takashicompany/jourkey/images/01.jpg

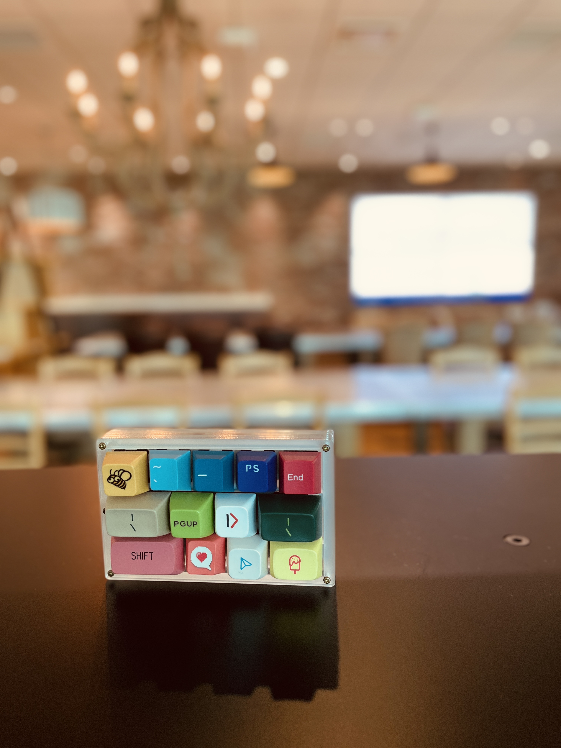
images/01.jpg
