takashicompany/jourkey/images/02.jpg

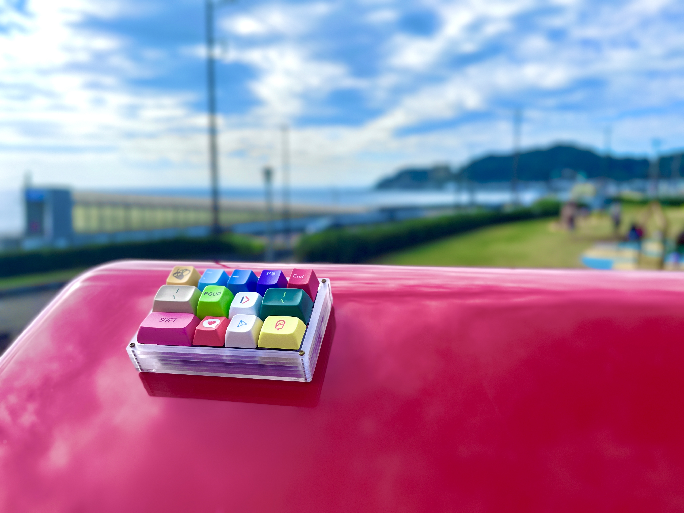
images/02.jpg
