takashicompany/jourkey/images/04.jpg

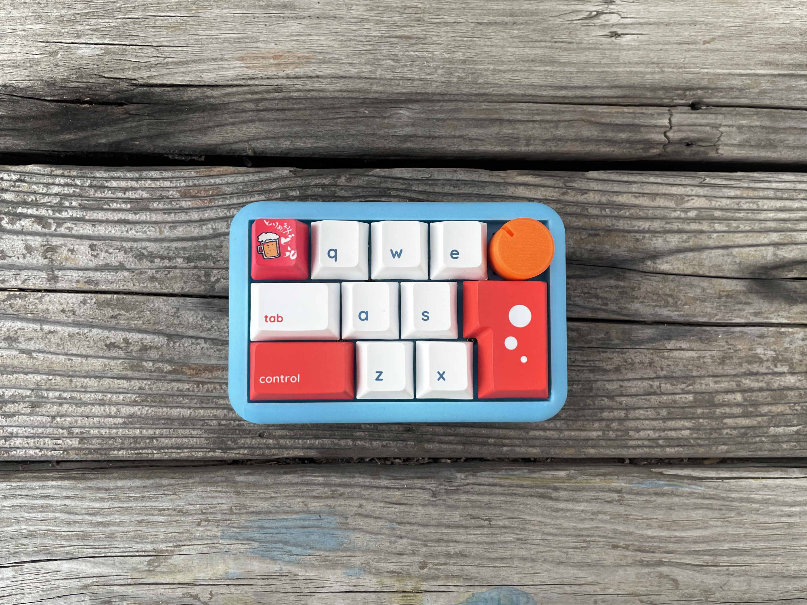
images/04.jpg
