takashicompany/jourkey/images/build/IMG_0001.jpg

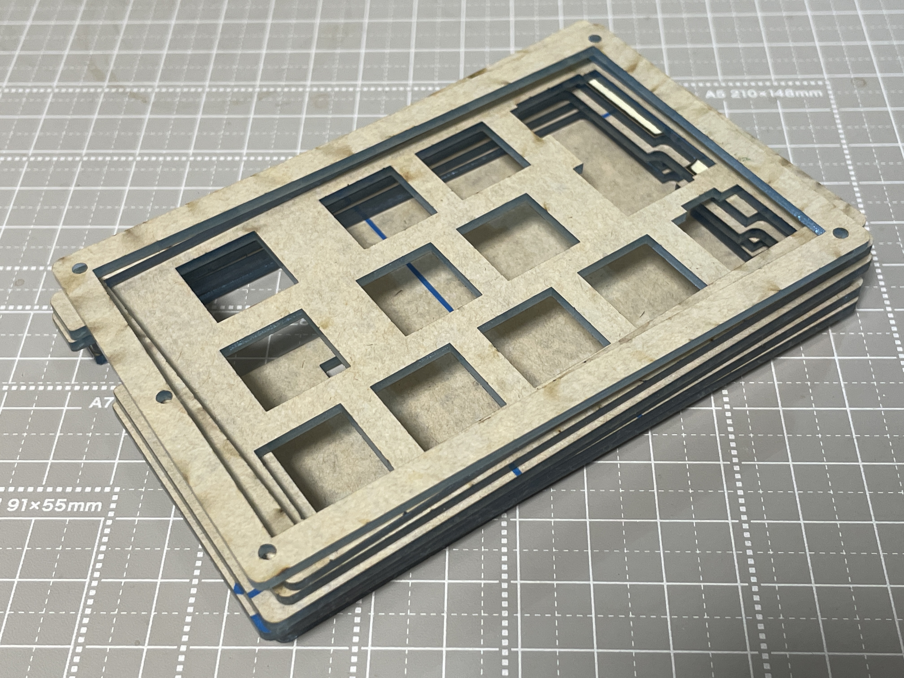
images/build/IMG_0001.jpg
