takashicompany/jourkey/images/build/IMG_0002.jpg

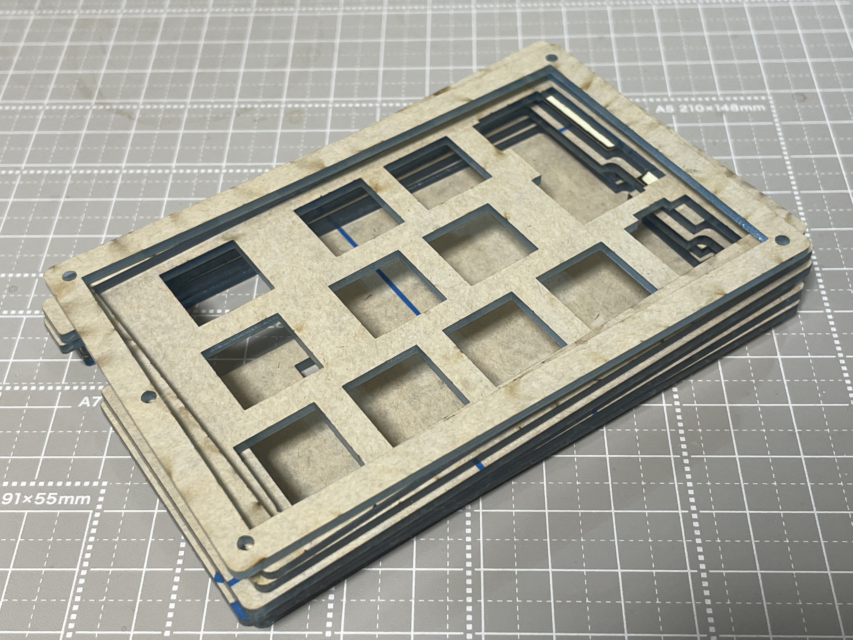
images/build/IMG_0002.jpg
