takashicompany/jourkey/images/build/IMG_0005.jpg

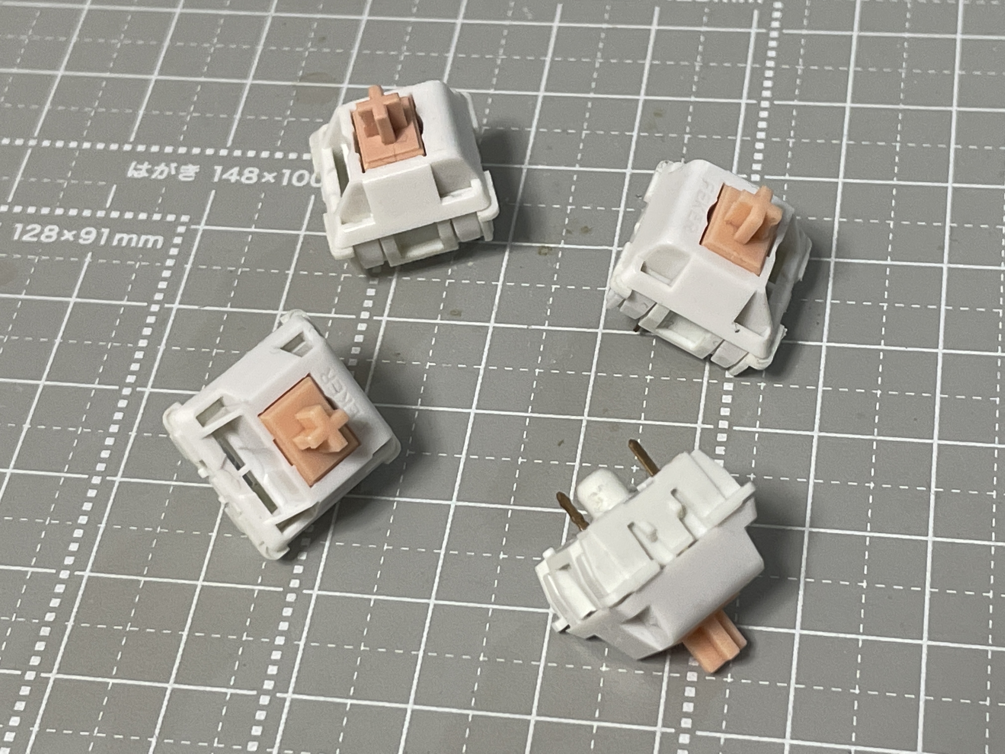
images/build/IMG_0005.jpg
