takashicompany/jourkey/images/build/IMG_0006.jpg

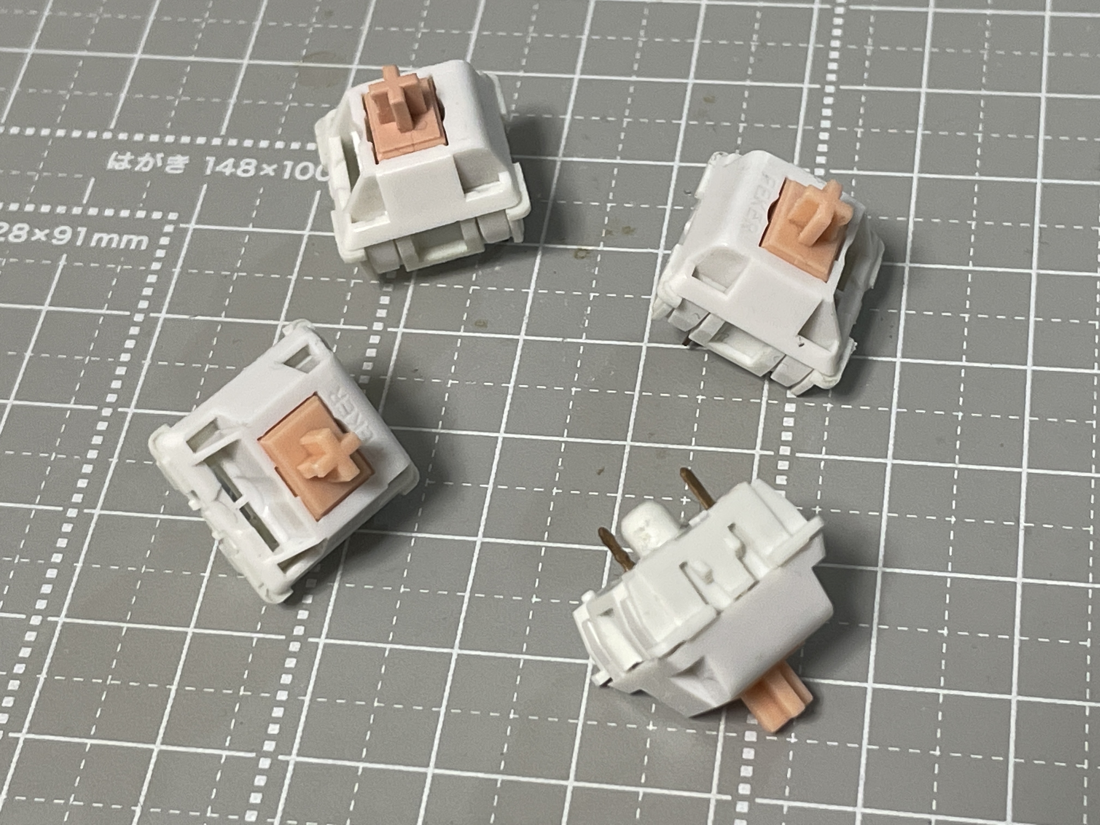
images/build/IMG_0006.jpg
