takashicompany/jourkey/images/build/IMG_0008.jpg

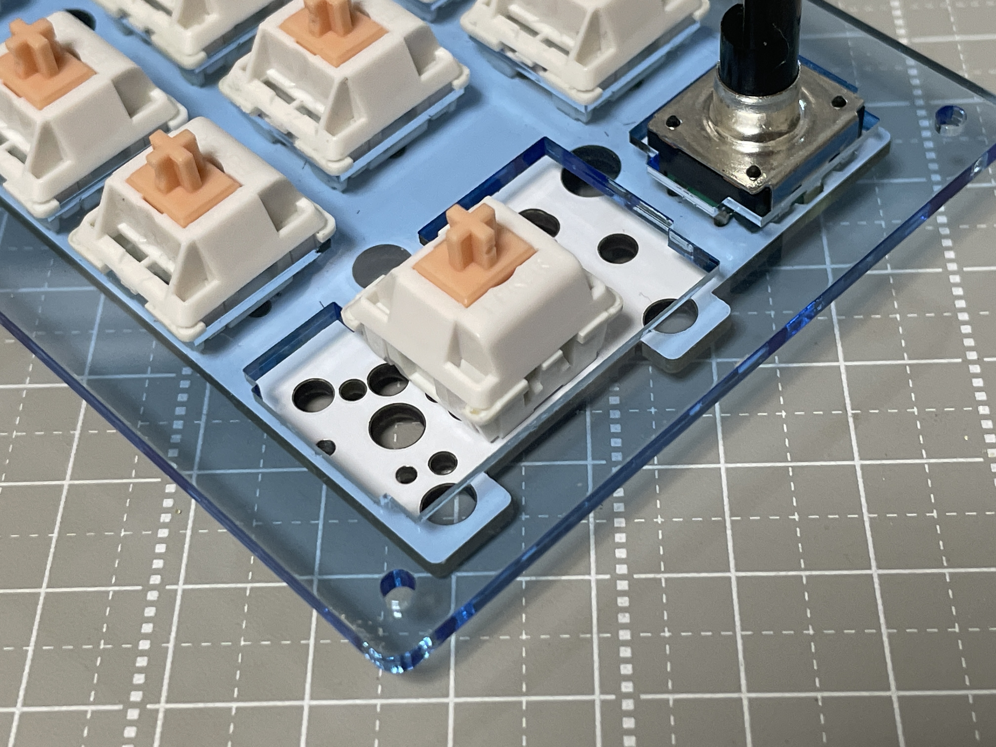
images/build/IMG_0008.jpg
