takashicompany/jourkey/images/build/IMG_0010.jpg

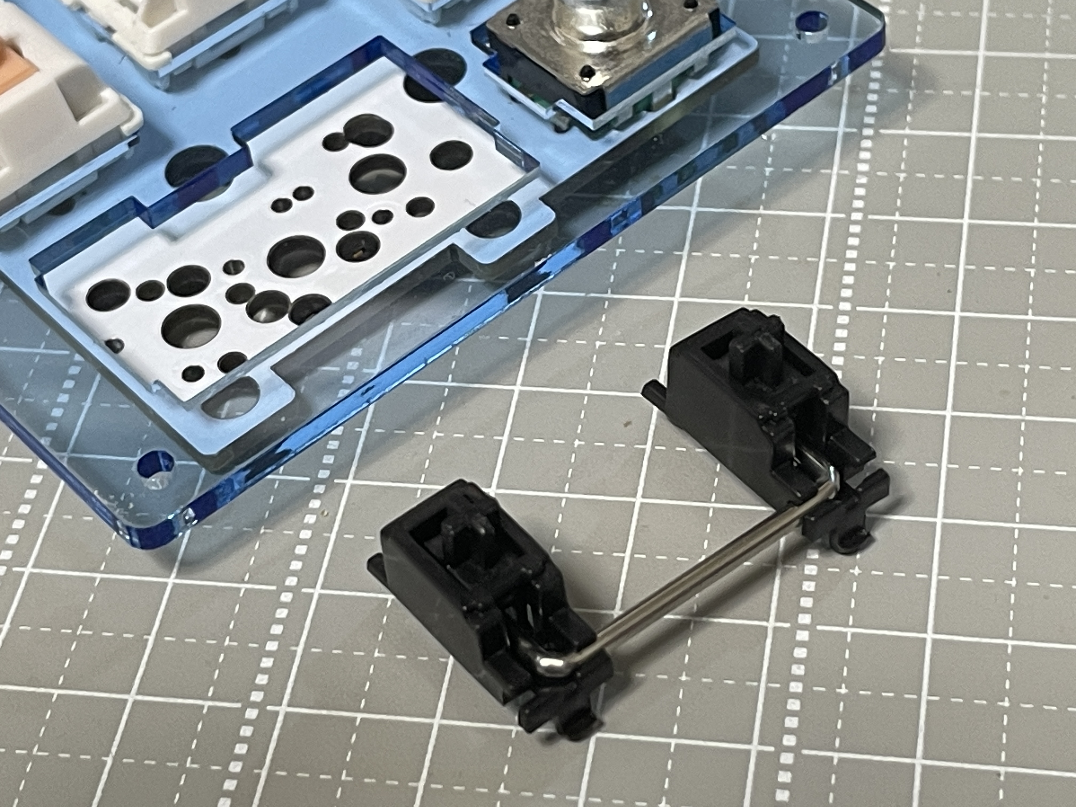
images/build/IMG_0010.jpg
