takashicompany/jourkey/images/build/IMG_0012.jpg

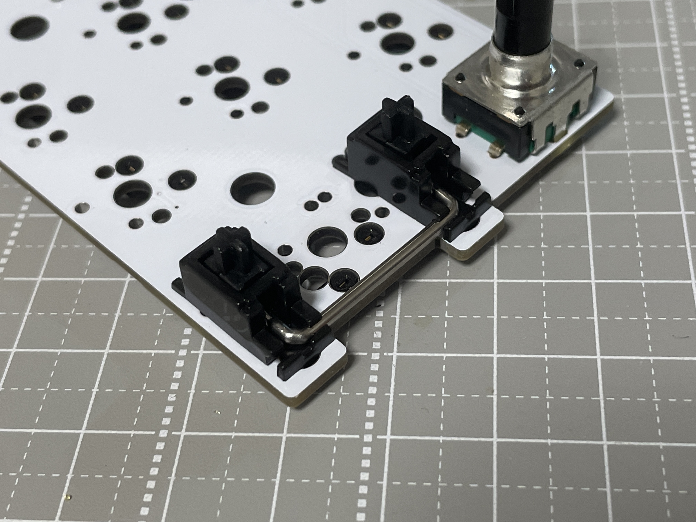
images/build/IMG_0012.jpg
