takashicompany/jourkey/images/build/IMG_0015.jpg

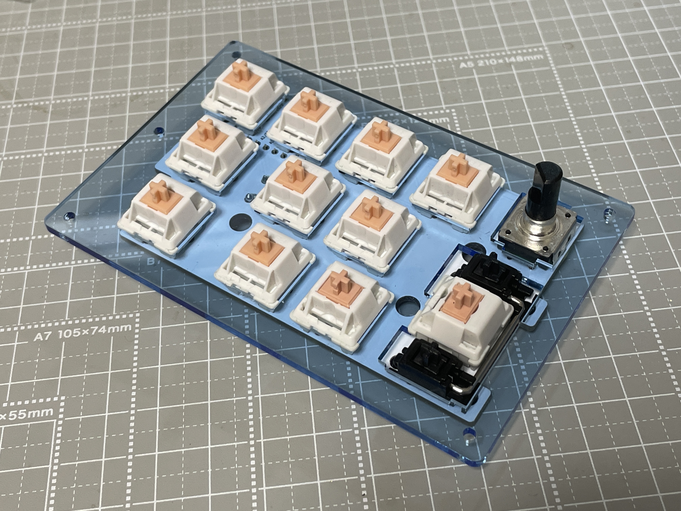
images/build/IMG_0015.jpg
