takashicompany/jourkey/images/build/IMG_0018.jpg

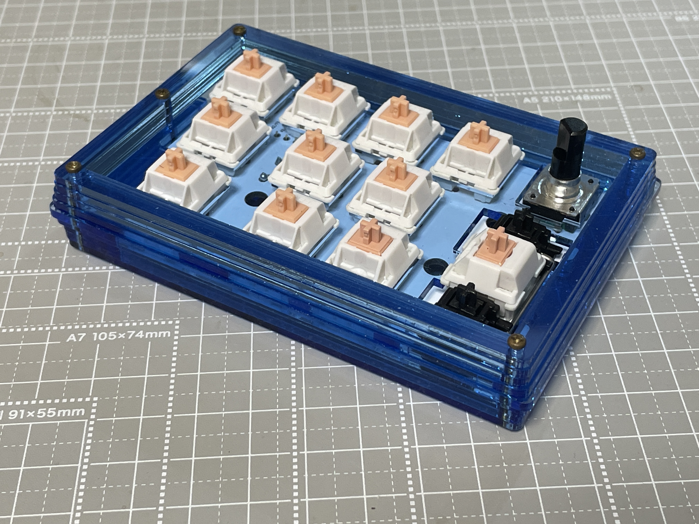
images/build/IMG_0018.jpg
