takashicompany/jourkey/images/build/IMG_0026.jpg

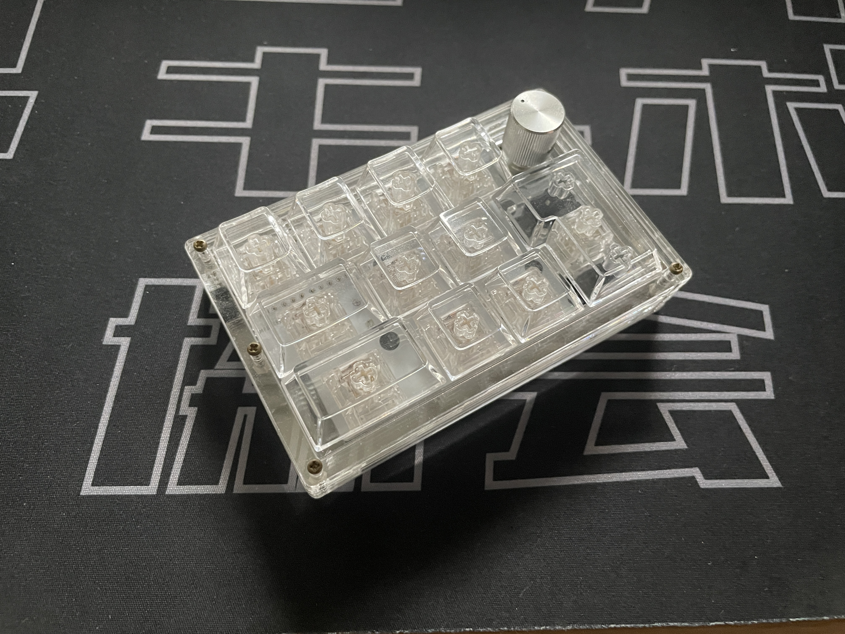
images/build/IMG_0026.jpg
