takashicompany/jourkey/images/build/IMG_0028.jpg

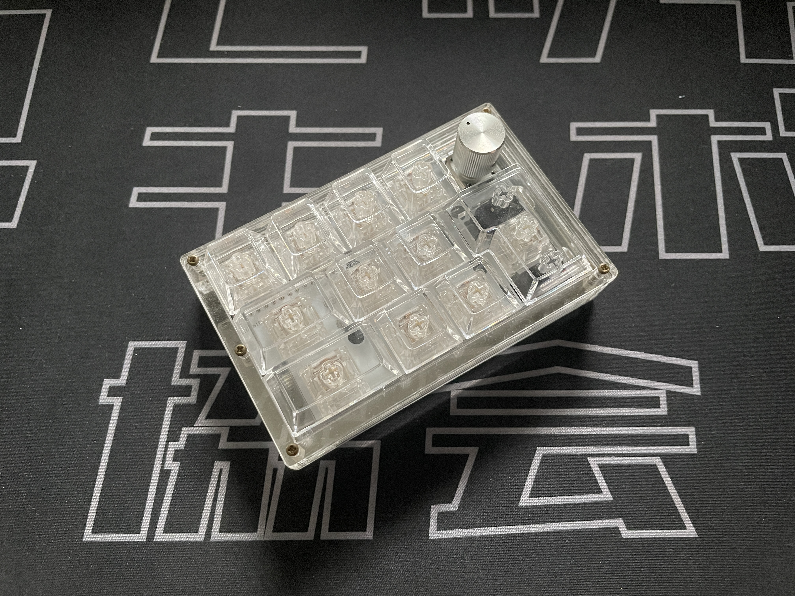
images/build/IMG_0028.jpg
