takashicompany/jourkey/images/build/IMG_9960.jpg

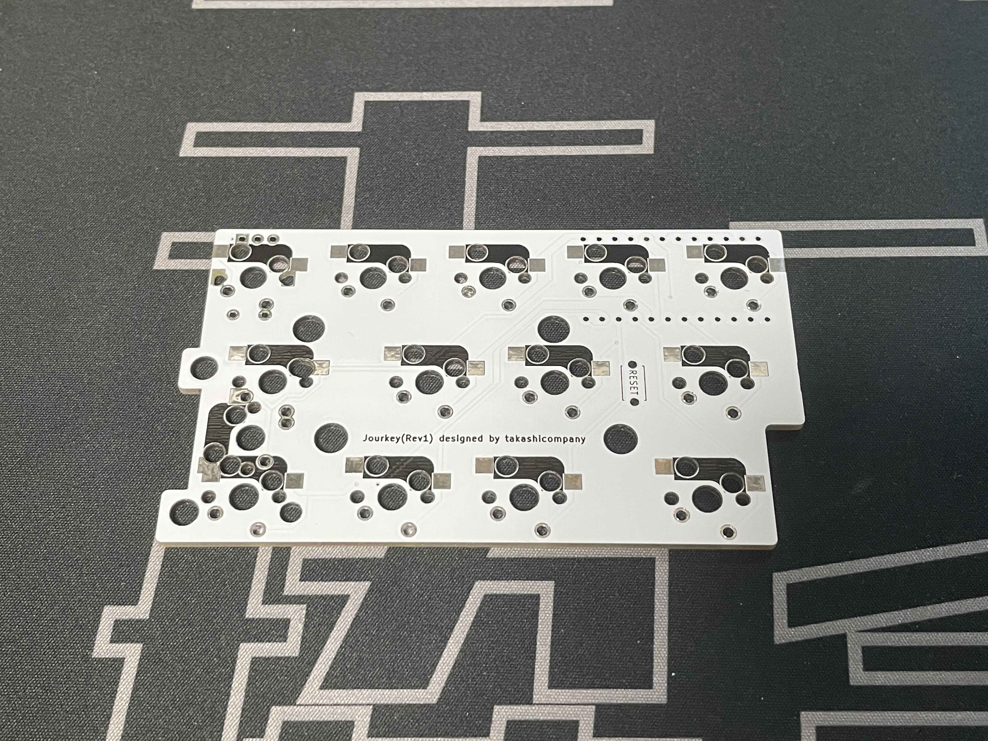
images/build/IMG_9960.jpg
