takashicompany/jourkey/images/build/IMG_9961.jpg

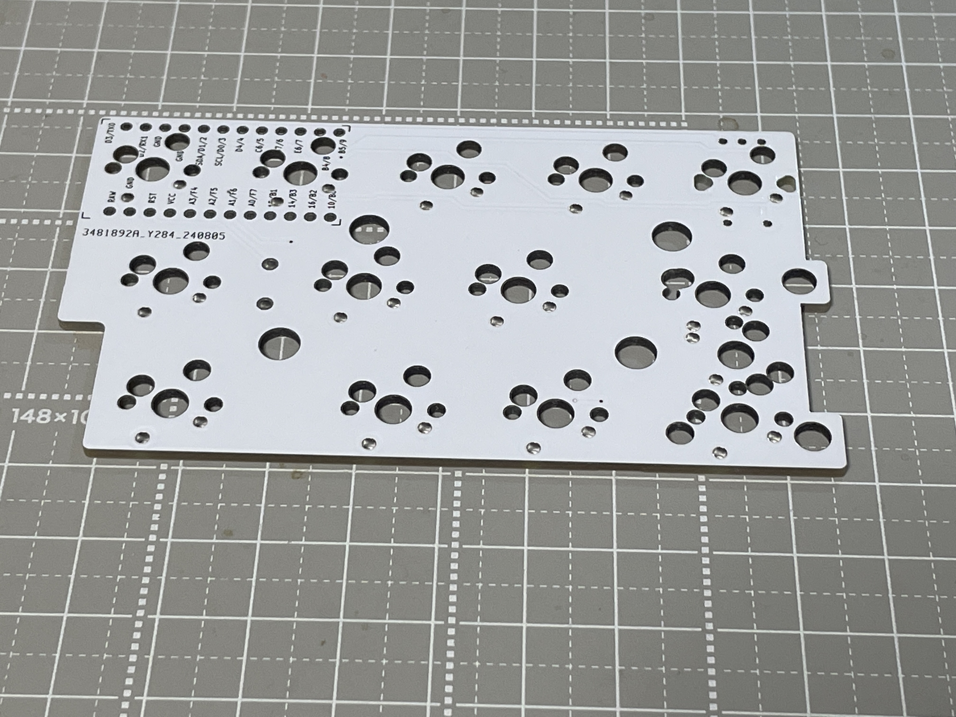
images/build/IMG_9961.jpg
