takashicompany/jourkey/images/build/IMG_9968.jpg

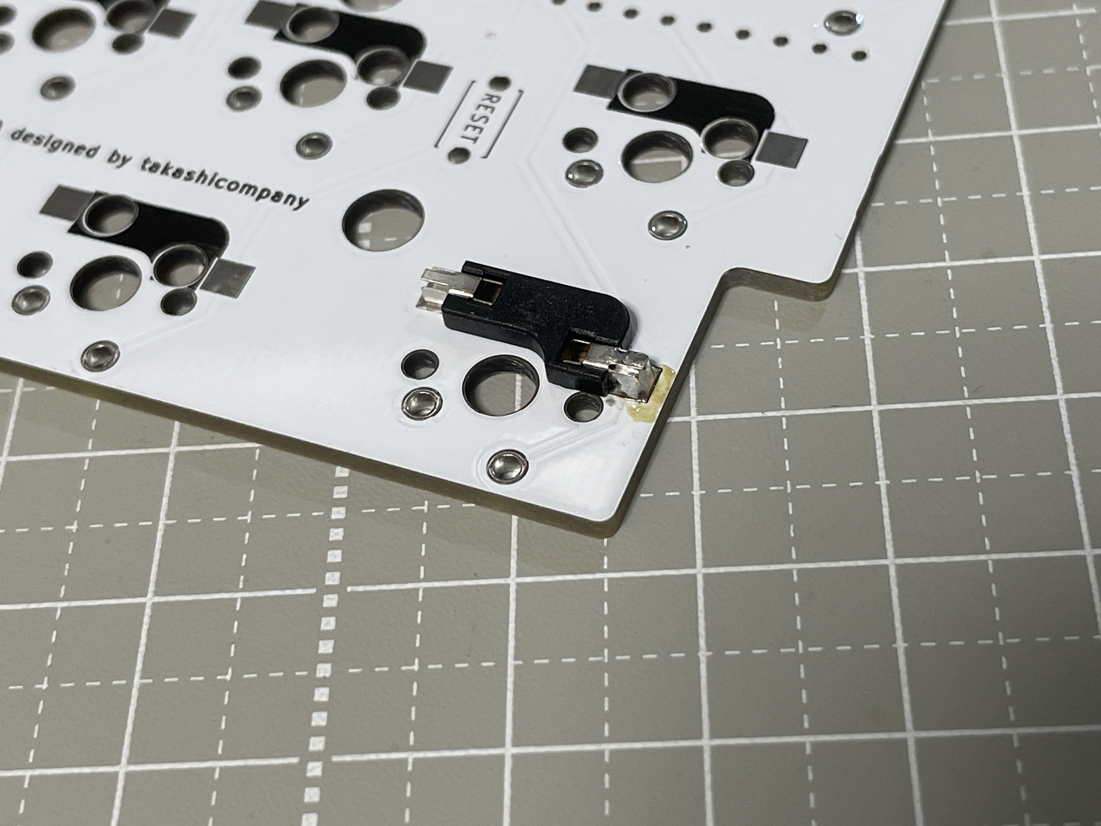
images/build/IMG_9968.jpg
