takashicompany/jourkey/images/build/IMG_9970.jpg

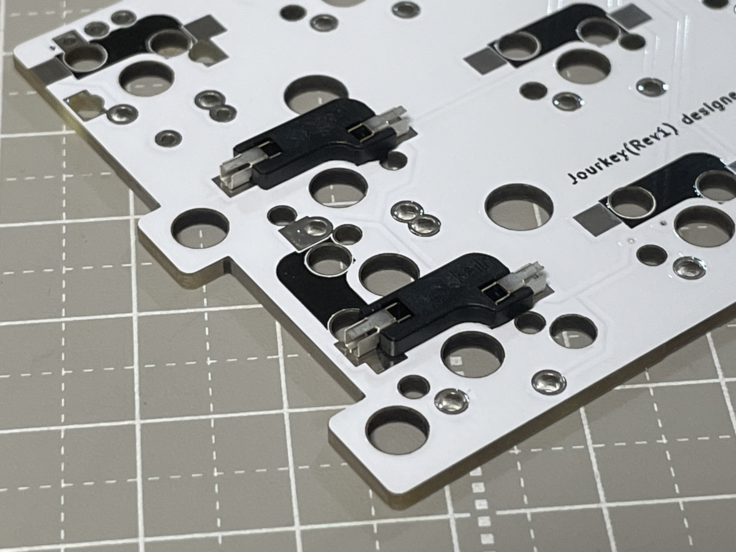
images/build/IMG_9970.jpg
