takashicompany/jourkey/images/build/IMG_9972.jpg

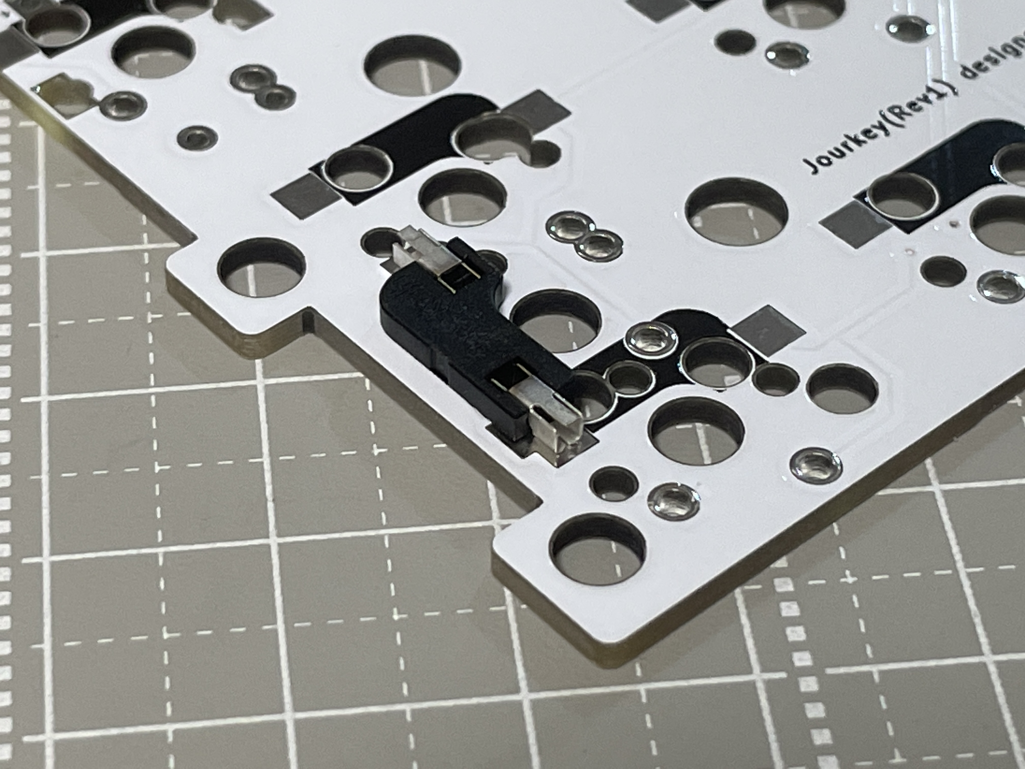
images/build/IMG_9972.jpg
