takashicompany/jourkey/images/build/IMG_9973.jpg

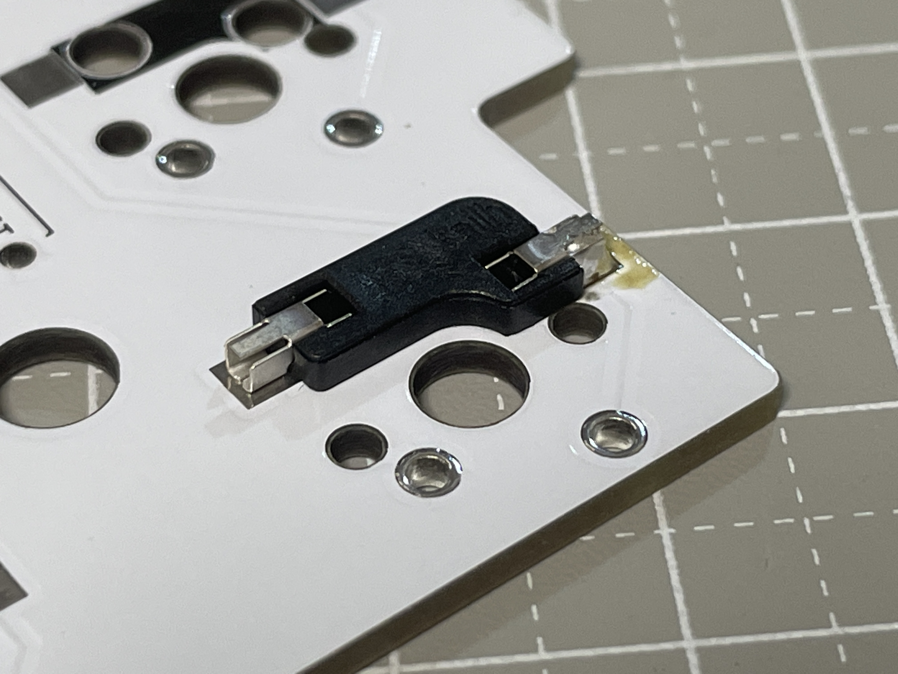
images/build/IMG_9973.jpg
