takashicompany/jourkey/images/build/IMG_9976.jpg

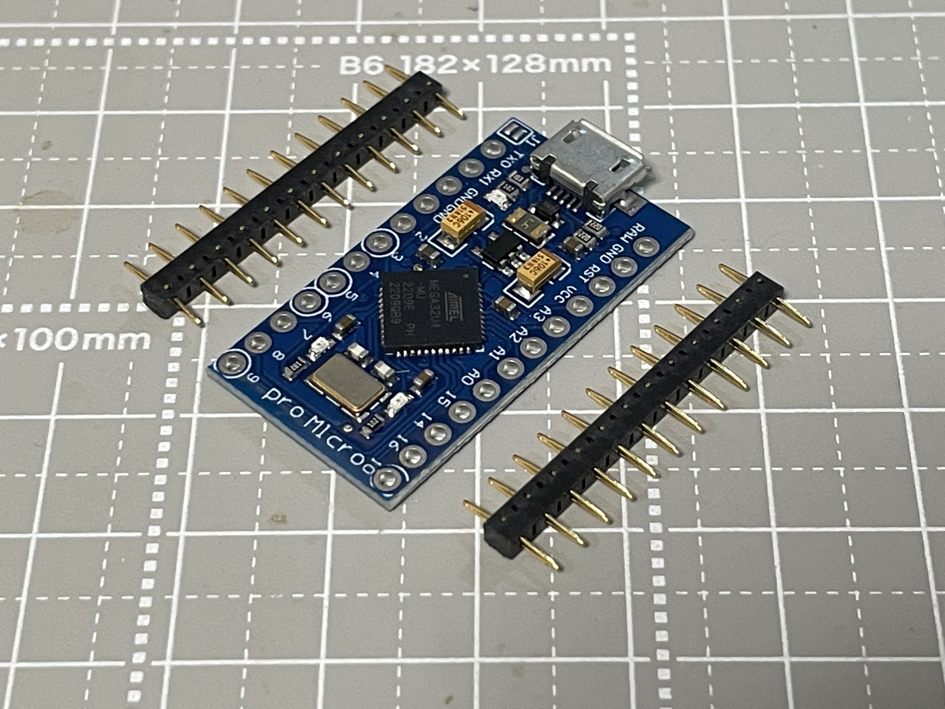
images/build/IMG_9976.jpg
