takashicompany/jourkey/images/build/IMG_9978.jpg

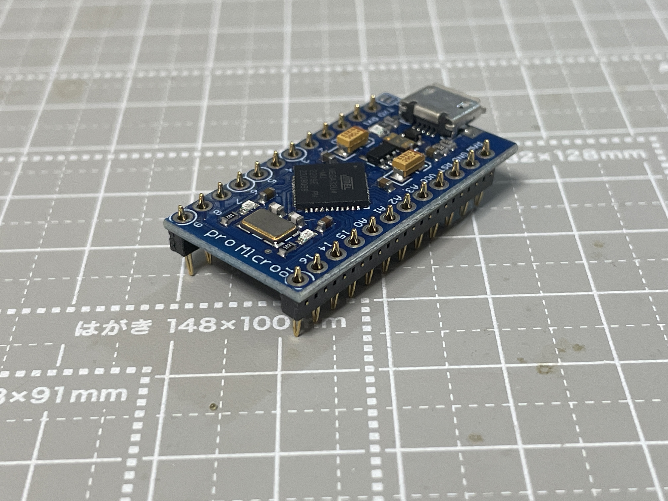
images/build/IMG_9978.jpg
