takashicompany/jourkey/images/build/IMG_9980.jpg

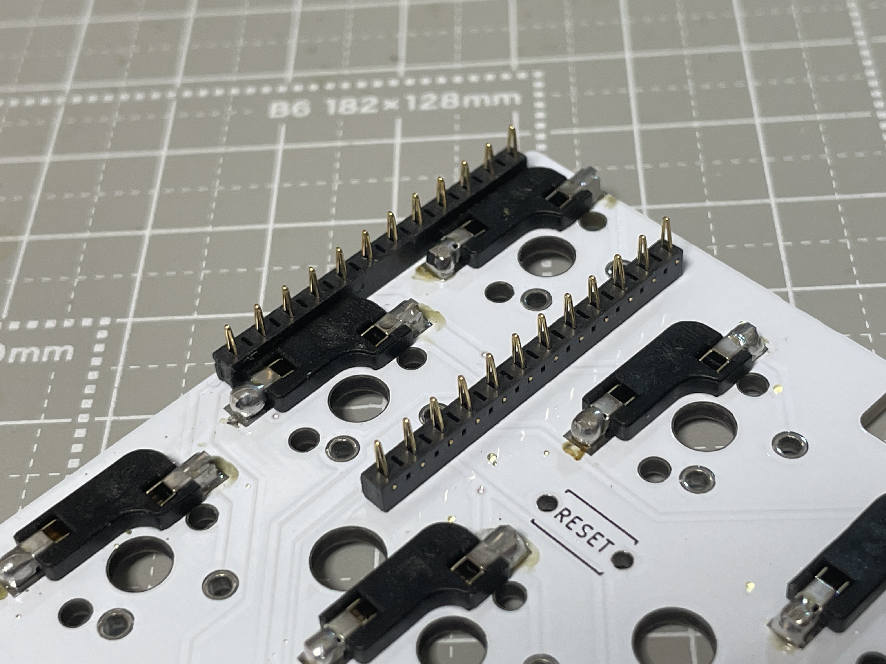
images/build/IMG_9980.jpg
