takashicompany/jourkey/images/build/IMG_9983.jpg

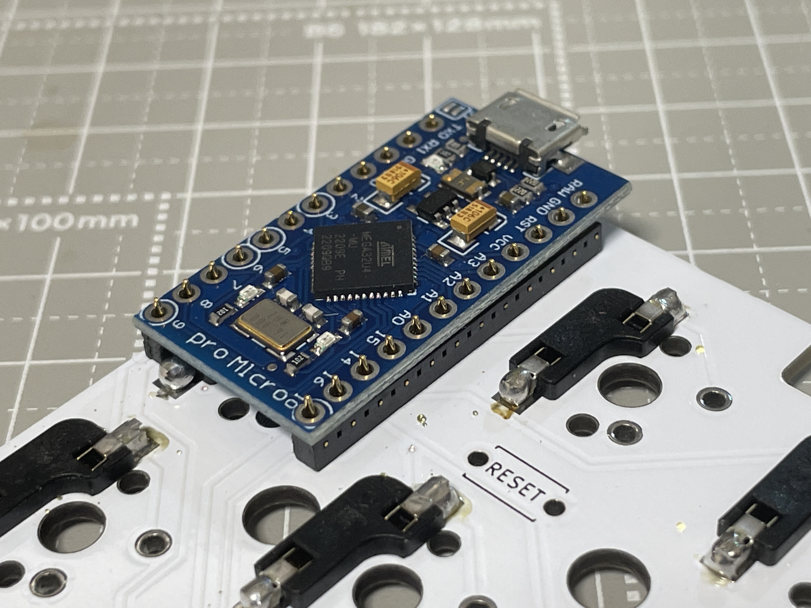
images/build/IMG_9983.jpg
