takashicompany/jourkey/images/build/IMG_9987.jpg

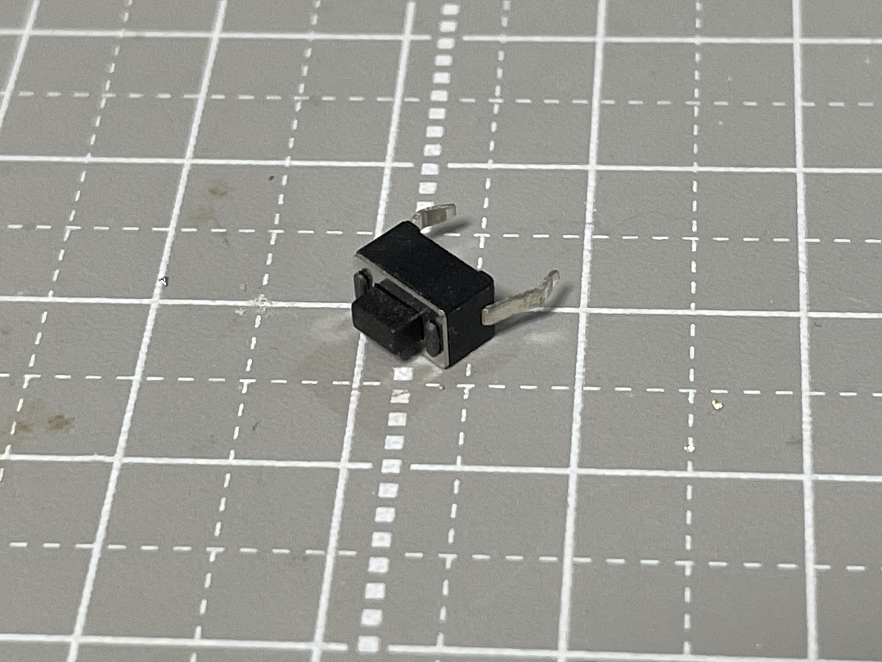
images/build/IMG_9987.jpg
