takashicompany/jourkey/images/build/IMG_9990.jpg

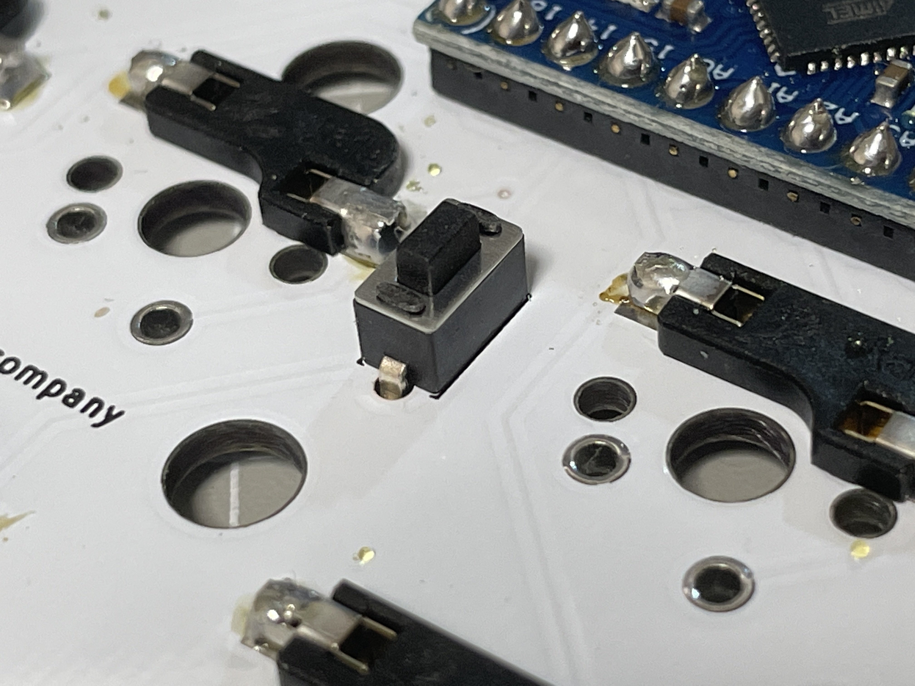
images/build/IMG_9990.jpg
