takashicompany/jourkey/images/build/IMG_9992.jpg

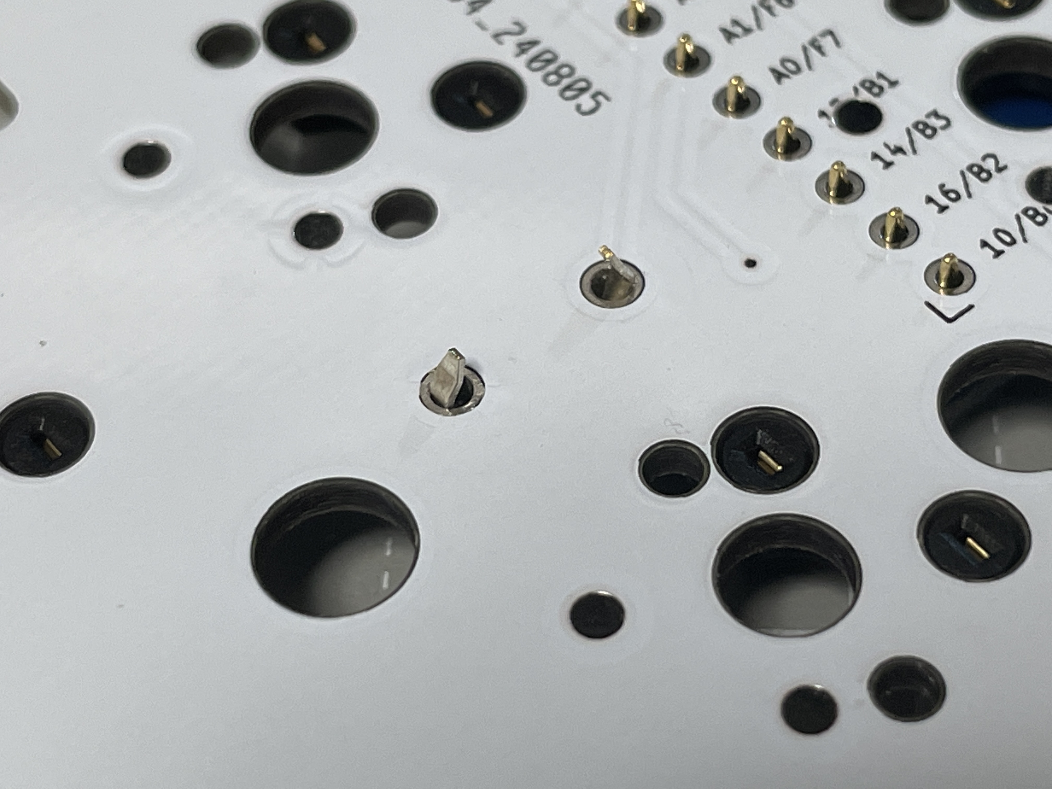
images/build/IMG_9992.jpg
