takashicompany/jourkey/images/build/IMG_9994.jpg

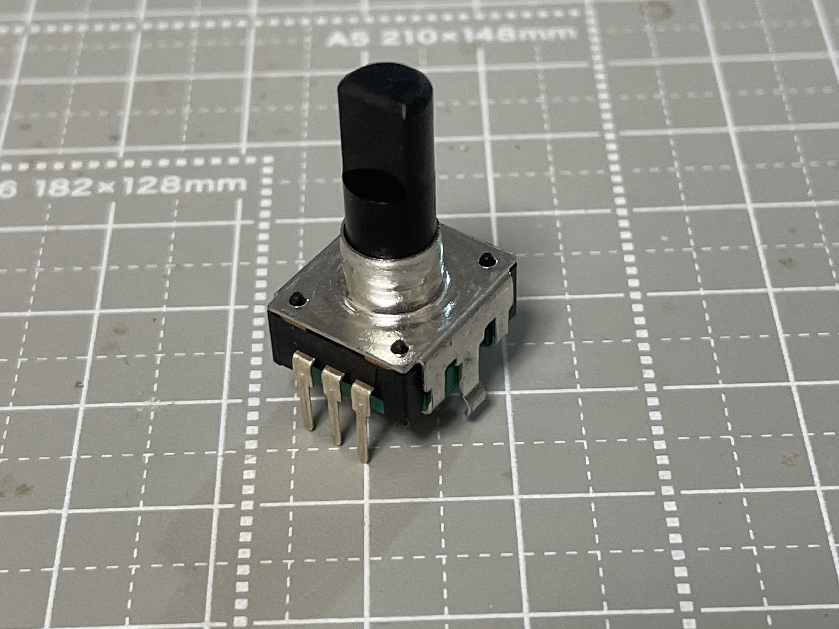
images/build/IMG_9994.jpg
