takashicompany/jourkey/images/build/IMG_9996.jpg

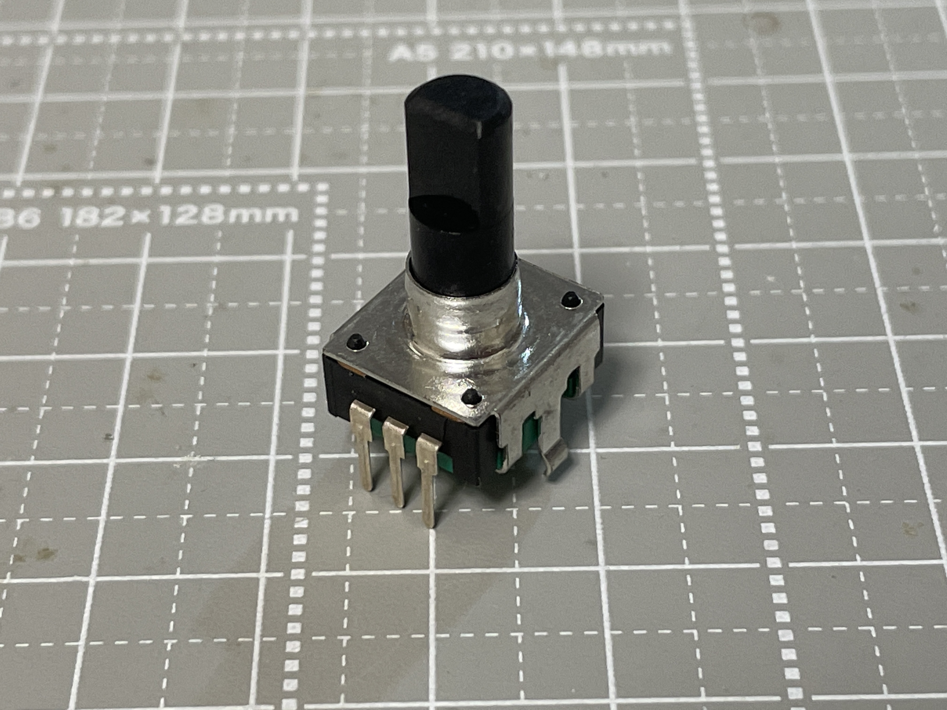
images/build/IMG_9996.jpg
