takashicompany/jourkey/images/build/IMG_9997.jpg

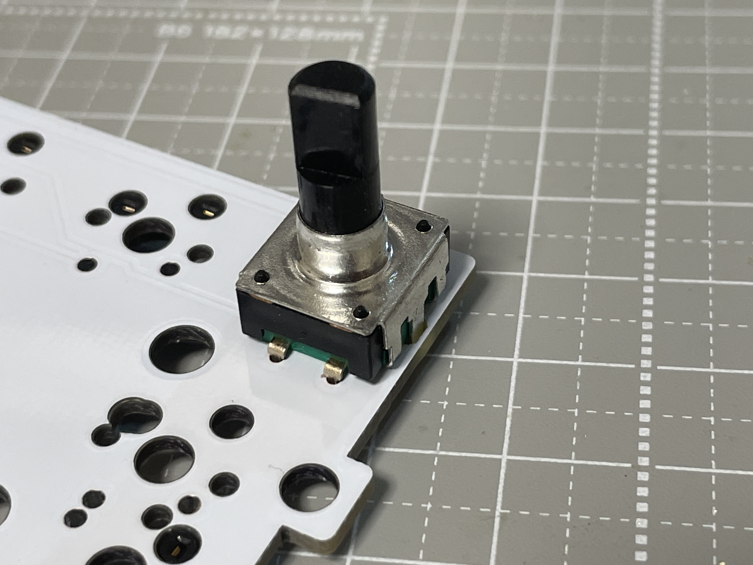
images/build/IMG_9997.jpg
